PowerEnterKey/PEKS48/img/S__109133847_0.jpg

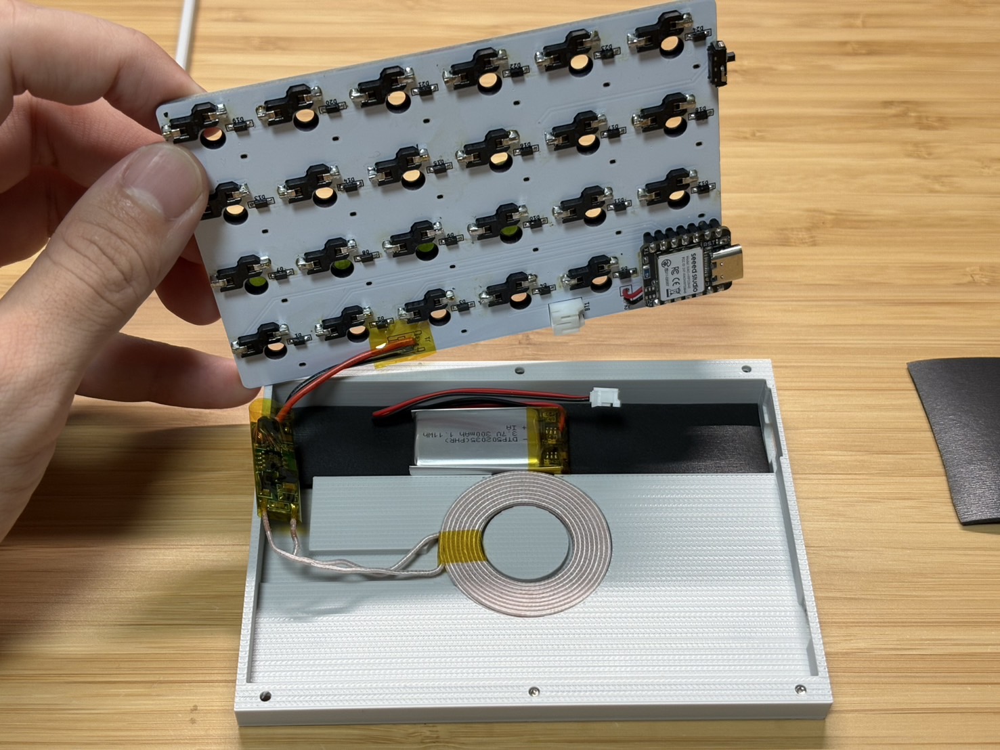
img/S__109133847_0.jpg
