PowerEnterKey/PEKS48/img/S__109133849_0.jpg

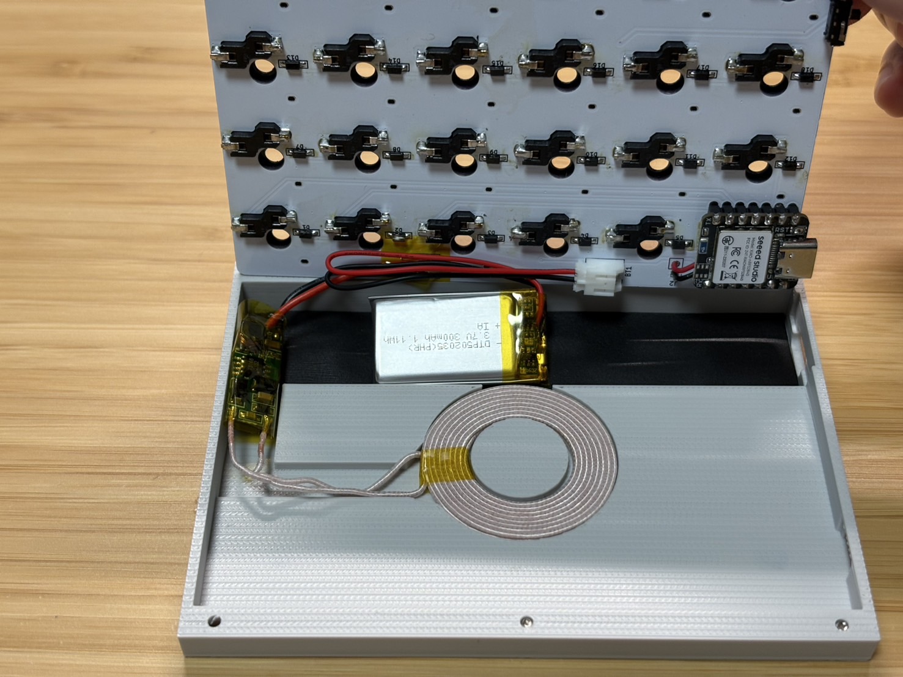
img/S__109133849_0.jpg
