PowerEnterKey/PEKS48/img/S__109133856_0.jpg

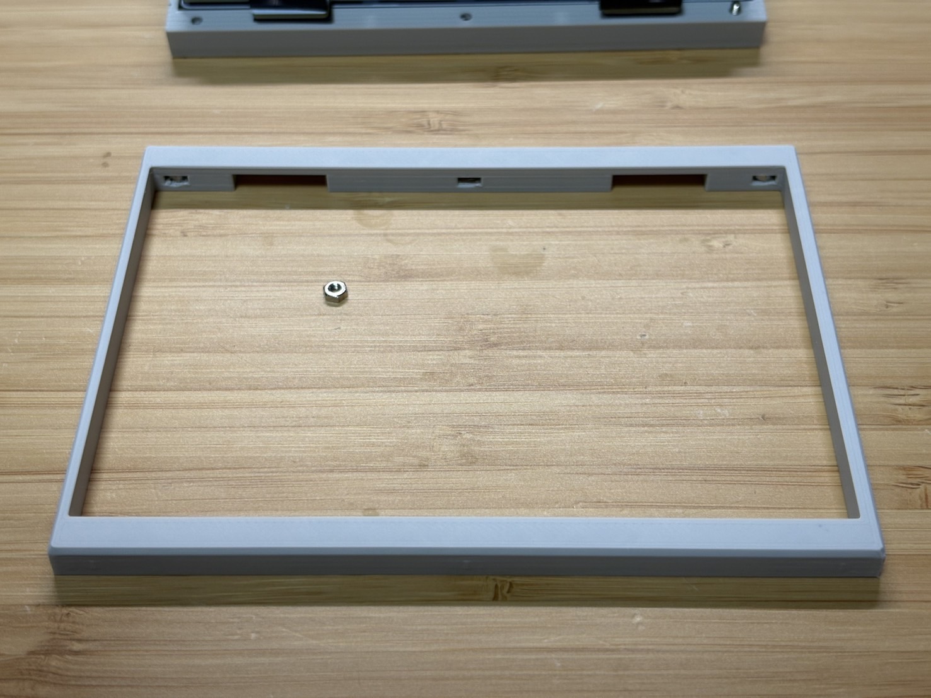
img/S__109133856_0.jpg
