PowerEnterKey/PEKS48/img/S__109133866_0.jpg

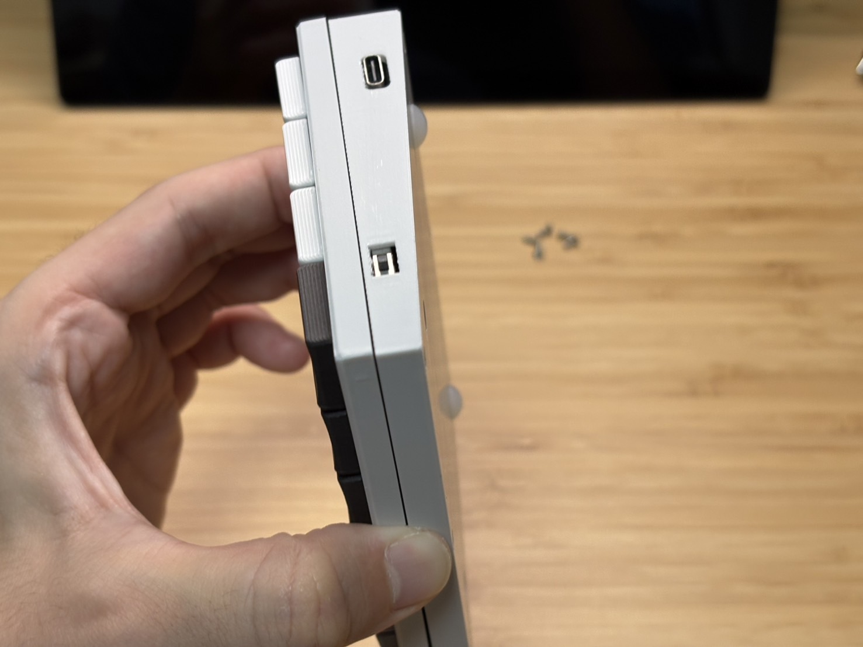
img/S__109133866_0.jpg
